Eraser2333/TD4CPU/图片/markdown/74HC74.png

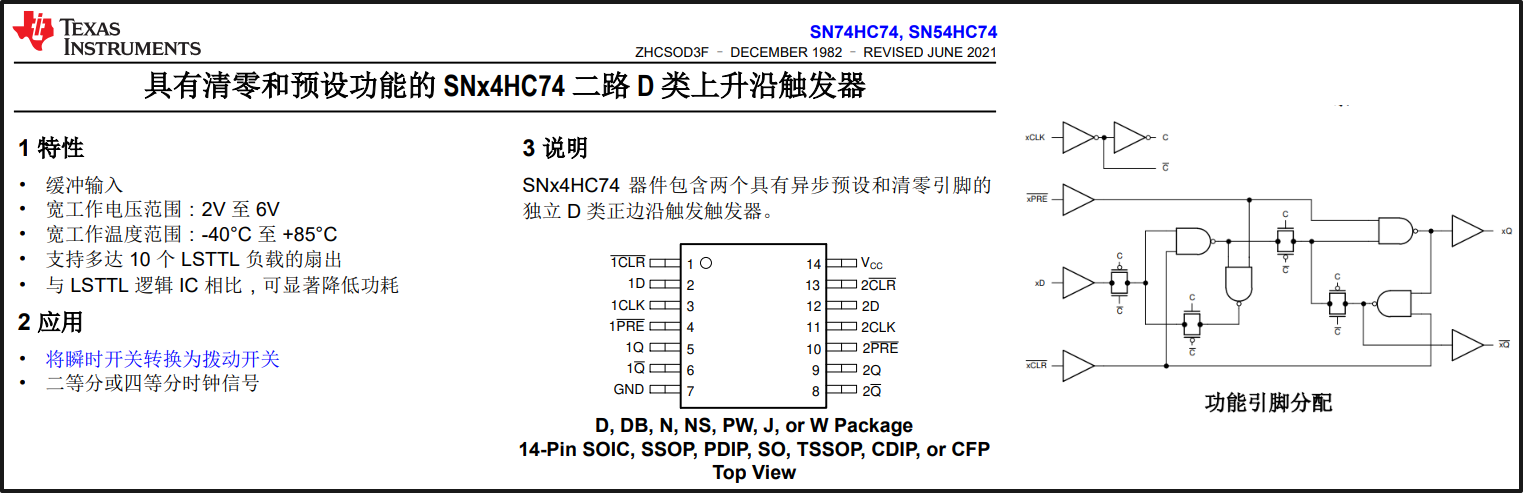
图片/markdown/74HC74.png
