Eraser2333/TD4CPU/图片/指令集讲解.png

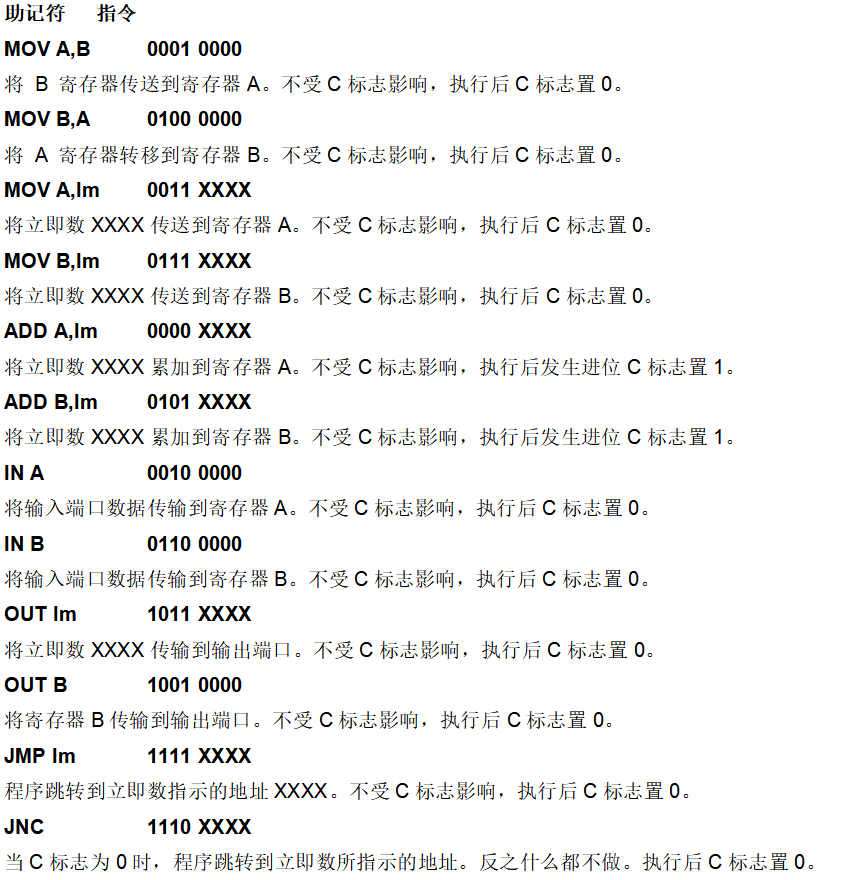
图片/指令集讲解.png
