Eraser2333/TD4CPU/图片/溯源二维码.png

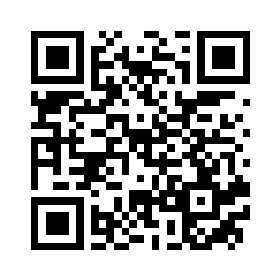
图片/溯源二维码.png
